DrMikeG/2023_pico_space_mushroom/Space_Mushroom___Full_6_DOFs_Space_Mouse_5739462/images/3dmouse.jpg

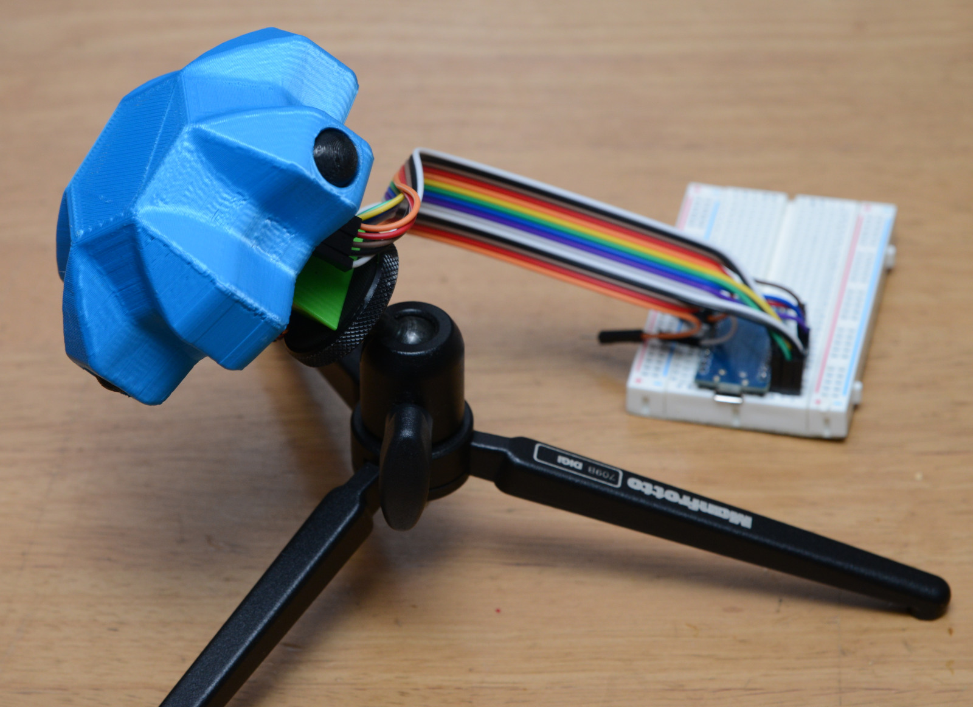
Space_Mushroom___Full_6_DOFs_Space_Mouse_5739462/images/3dmouse.jpg
