DrMikeG/2023_pico_space_mushroom/Space_Mushroom___Full_6_DOFs_Space_Mouse_5739462/images/_2022-12-24_12.27.17.jpg

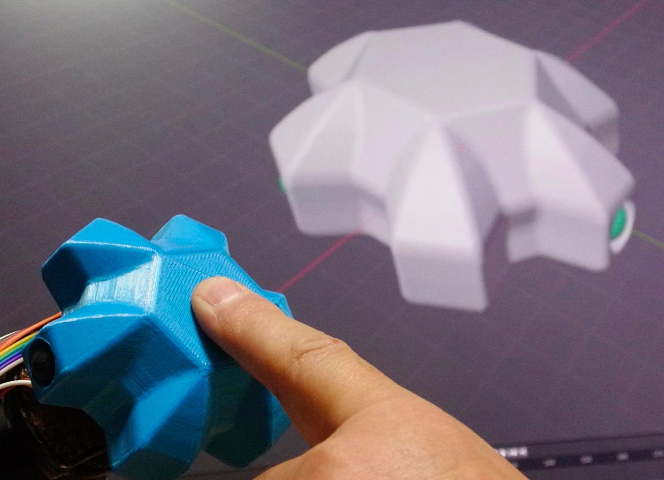
Space_Mushroom___Full_6_DOFs_Space_Mouse_5739462/images/_2022-12-24_12.27.17.jpg
