DrMikeG/2023_pico_space_mushroom/Space_Mushroom___Full_6_DOFs_Space_Mouse_5739462/images/ball-joint.png

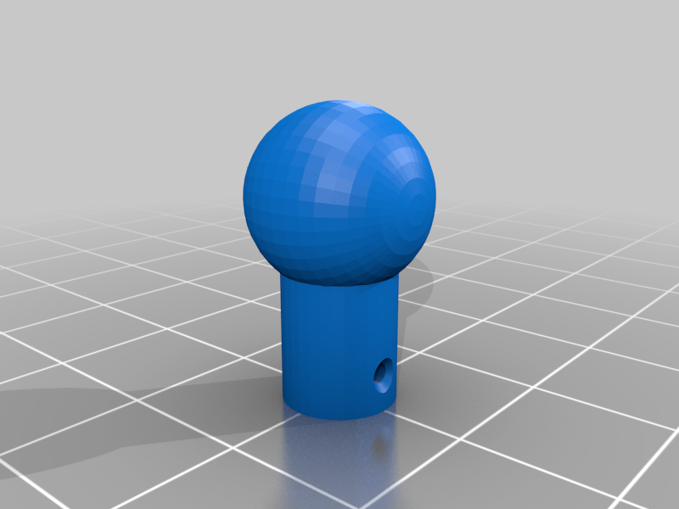
Space_Mushroom___Full_6_DOFs_Space_Mouse_5739462/images/ball-joint.png
