DrMikeG/2023_pico_space_mushroom/parts/mounting_lid_right_03.3mf

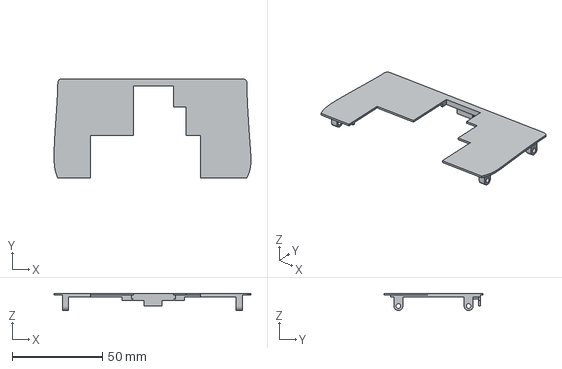
[picture p26: CAD file, 2023-02-21]
parts/mounting_lid_right_03.3mf
109.4 x 55.0 x 9.50 mm
