DrMikeG/2023_pico_space_mushroom/parts/Mounting_ADC_layer_04.3mf

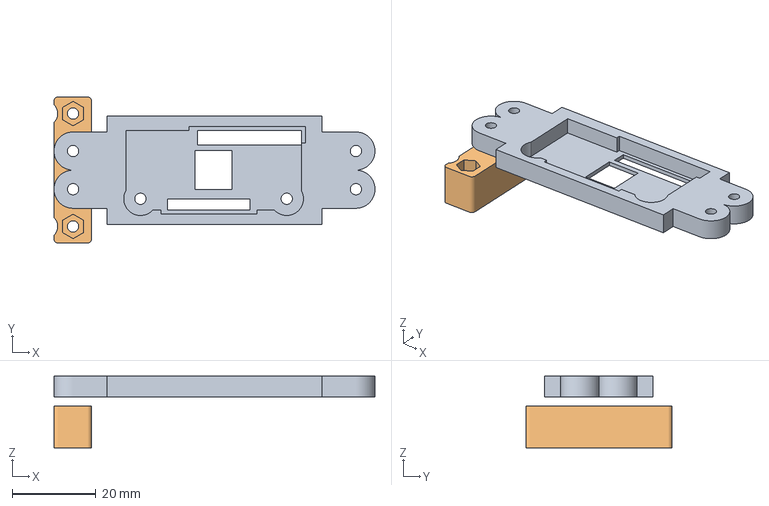
[picture p27: CAD file, 2023-02-15]
parts/Mounting_ADC_layer_04.3mf
76.8 x 35.0 x 17.2 mm
Mounting_ADC_layer_04 x 2
