DrMikeG/2023_pico_space_mushroom/parts/mounting_subbase_01.3mf

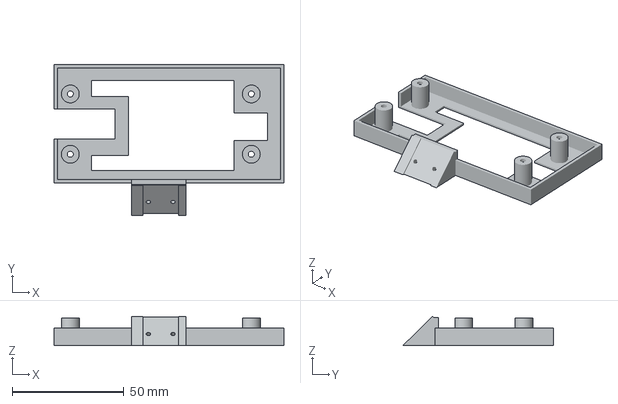
[picture p28: CAD file, 2023-02-15]
parts/mounting_subbase_01.3mf
103.0 x 67.4 x 13.2 mm
