DrMikeG/2023_pico_space_mushroom/parts/mounting_lid_right_02.3mf

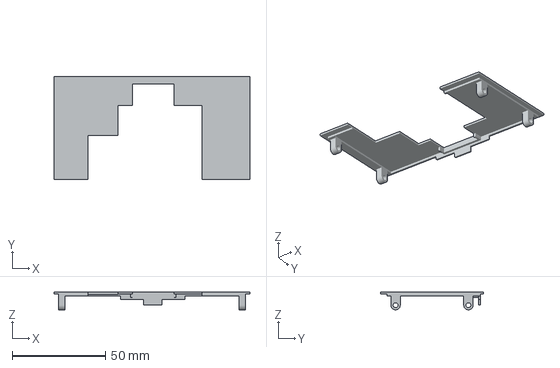
[picture p29: CAD file, 2023-02-15]
parts/mounting_lid_right_02.3mf
105.0 x 55.0 x 9.50 mm
