DrMikeG/2023_pico_space_mushroom/parts/Mounting_ProtoLayer00_01.3mf

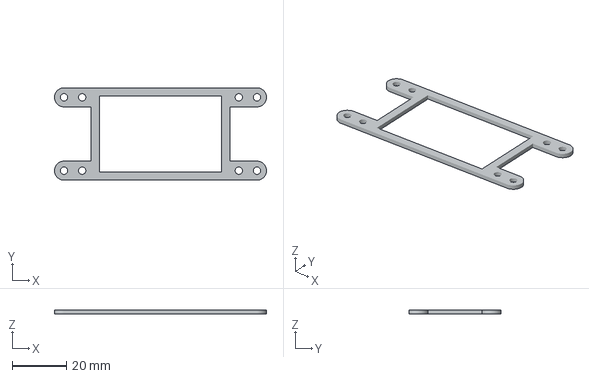
[picture p30: CAD file, 2023-02-15]
parts/Mounting_ProtoLayer00_01.3mf
78.1 x 34.0 x 1.50 mm
