DrMikeG/2023_pico_space_mushroom/parts/mounting_subbase_03.3mf

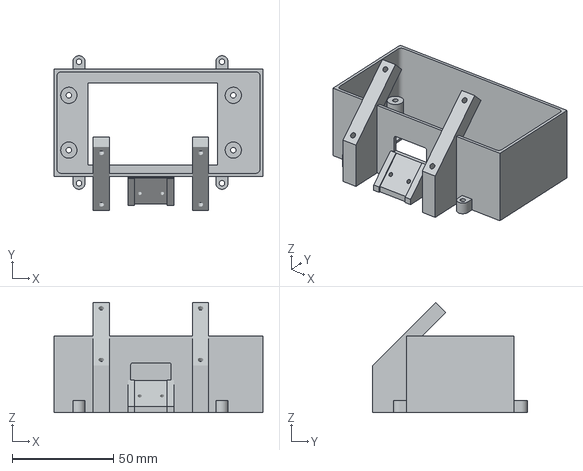
[picture p31: CAD file, 2023-02-15]
parts/mounting_subbase_03.3mf
103.0 x 76.3 x 54.3 mm
