DrMikeG/2023_pico_space_mushroom/parts/mounting_subbase_02.3mf

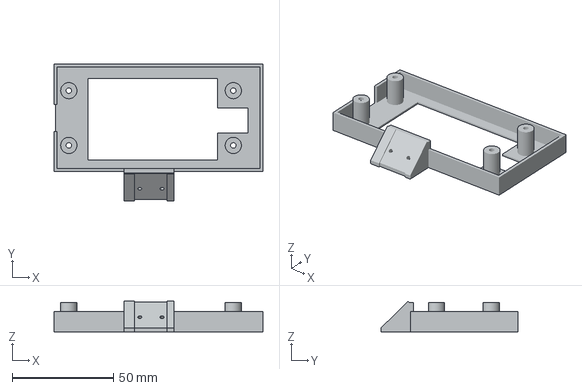
[picture p32: CAD file, 2023-02-15]
parts/mounting_subbase_02.3mf
103.0 x 67.4 x 15.2 mm
