DrMikeG/2023_pico_space_mushroom/parts/Mounting_ProtoLayer00_03.3mf

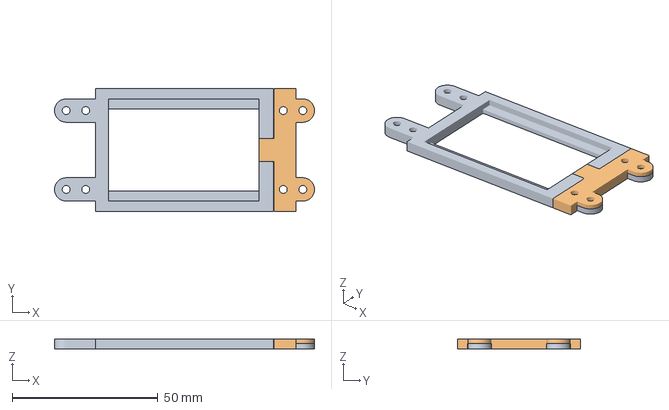
[picture p33: CAD file, 2023-02-15]
parts/Mounting_ProtoLayer00_03.3mf
89.1 x 42.0 x 3.50 mm
Mounting_ProtoLayer00_03 x 2
