DrMikeG/2023_pico_space_mushroom/parts/Mounting_ADC_layer_03.3mf

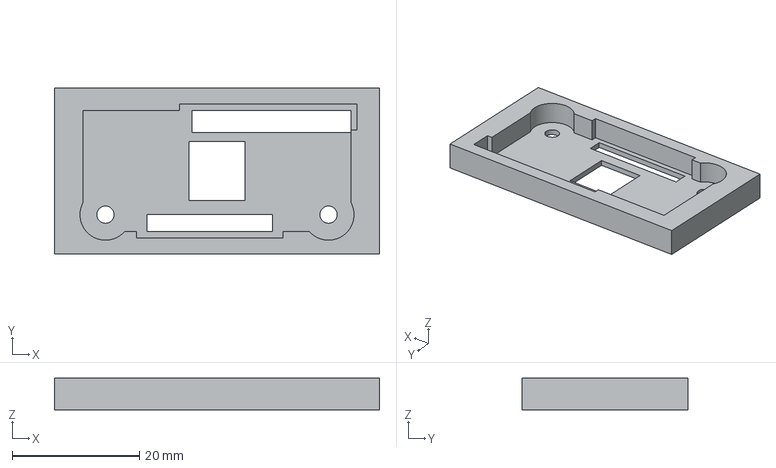
[picture p34: CAD file, 2023-02-15]
parts/Mounting_ADC_layer_03.3mf
51.0 x 26.0 x 5.00 mm
