DrMikeG/2023_pico_space_mushroom/parts/Mounting_ADC_layer_06.3mf

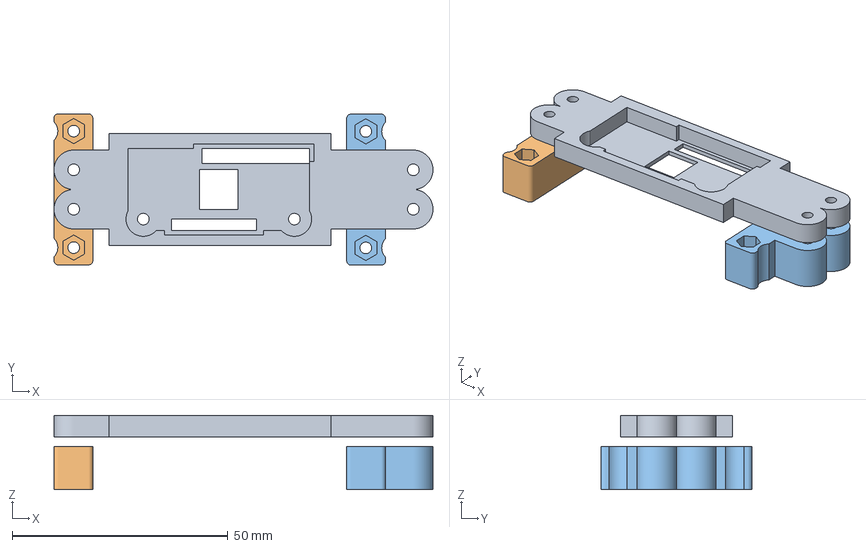
[picture p35: CAD file, 2023-02-15]
parts/Mounting_ADC_layer_06.3mf
87.8 x 35.1 x 17.2 mm
Mounting_ADC_layer_06 x 3
