DrMikeG/2023_pico_space_mushroom/parts/mounting_feet_01.3mf

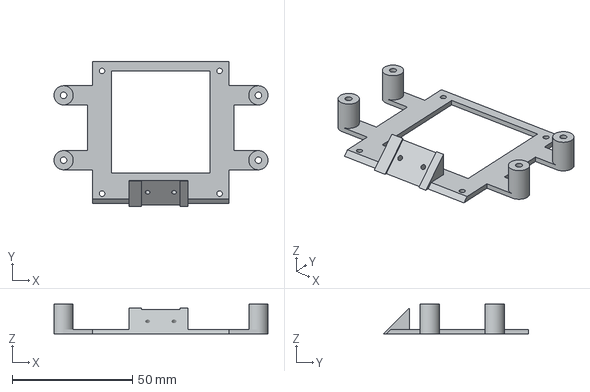
[picture p36: CAD file, 2023-02-15]
parts/mounting_feet_01.3mf
89.1 x 60.5 x 12.4 mm
