DrMikeG/2023_pico_space_mushroom/parts/mounting_subbase_04.3mf

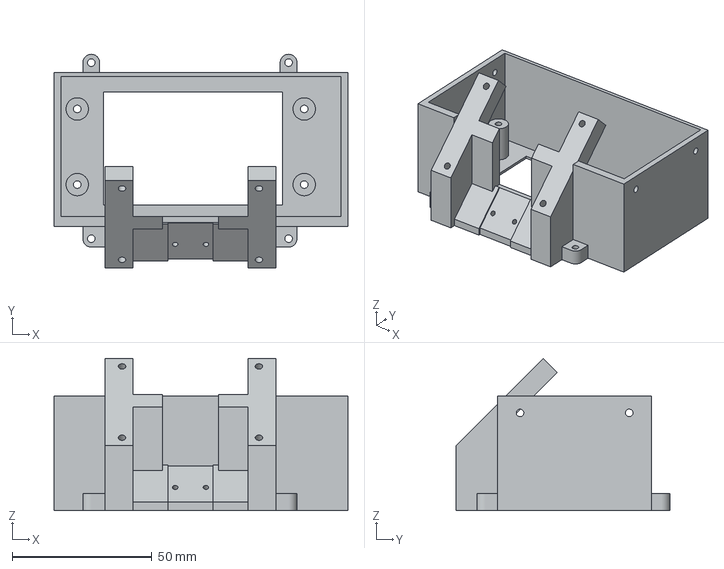
[picture p37: CAD file, 2023-02-15]
parts/mounting_subbase_04.3mf
105.0 x 76.3 x 54.3 mm
