DrMikeG/2023_pico_space_mushroom/parts/Mounting_ProtoLayer01_02.3mf

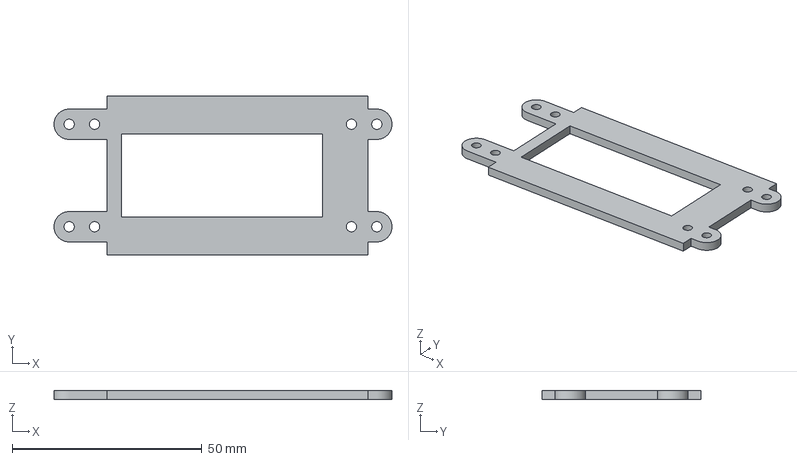
[picture p38: CAD file, 2023-02-15]
parts/Mounting_ProtoLayer01_02.3mf
89.1 x 42.0 x 2.50 mm
