DrMikeG/2023_pico_space_mushroom/parts/Mounting_ProtoLayer01_01.3mf

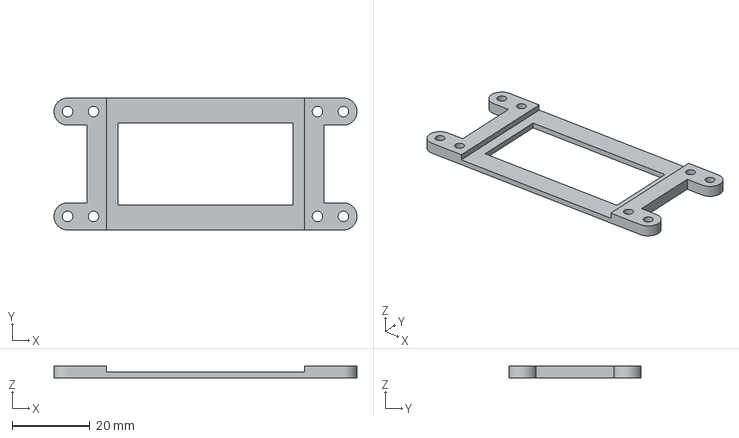
[picture p39: CAD file, 2023-02-15]
parts/Mounting_ProtoLayer01_01.3mf
78.1 x 34.0 x 3.10 mm
