DrMikeG/2023_pico_space_mushroom/parts/mounting_lid_right_01.3mf

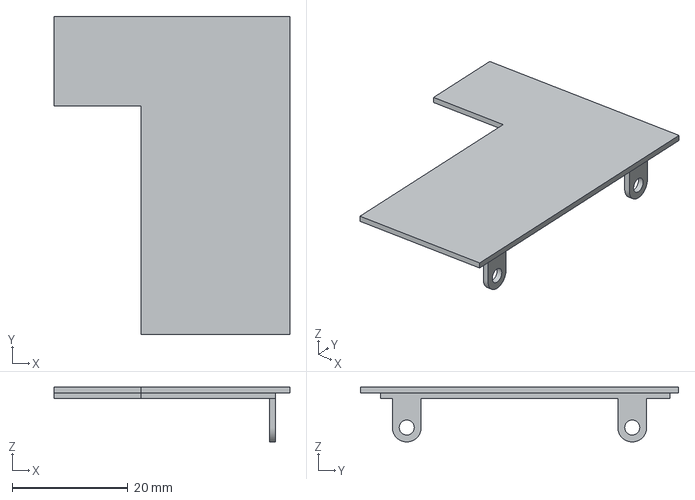
[picture p40: CAD file, 2023-02-15]
parts/mounting_lid_right_01.3mf
40.8 x 55.0 x 9.50 mm
