DrMikeG/2023_pico_space_mushroom/parts/Mounting_ProtoLayer00_02.3mf

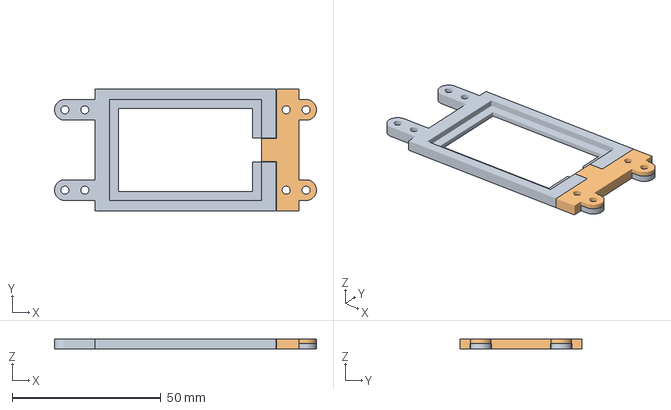
[picture p41: CAD file, 2023-02-15]
parts/Mounting_ProtoLayer00_02.3mf
88.1 x 41.0 x 3.50 mm
Mounting_ProtoLayer00_02 x 2
