DrMikeG/2023_pico_space_mushroom/parts/led_mount_03.3mf

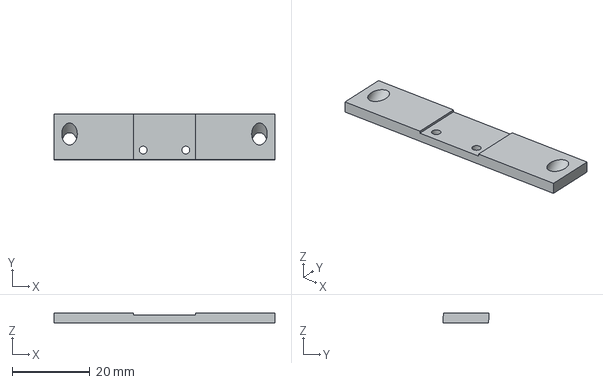
[picture p42: CAD file, 2023-02-02]
parts/led_mount_03.3mf
56.9 x 11.7 x 2.53 mm
