DrMikeG/2023_pico_space_mushroom/parts/min_base_support_02.3mf

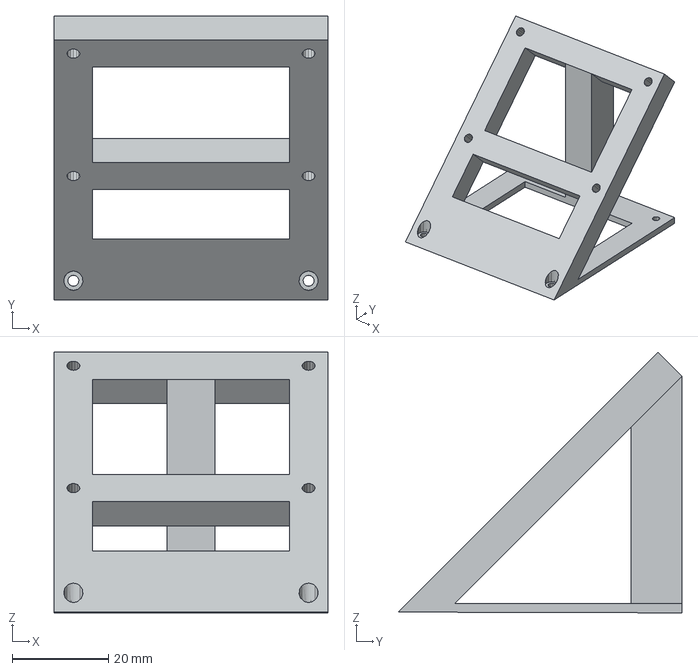
[picture p43: CAD file, 2023-01-13]
parts/min_base_support_02.3mf
56.9 x 59.1 x 54.2 mm
