DrMikeG/2023_pico_space_mushroom/parts/Thumbstick.3mf

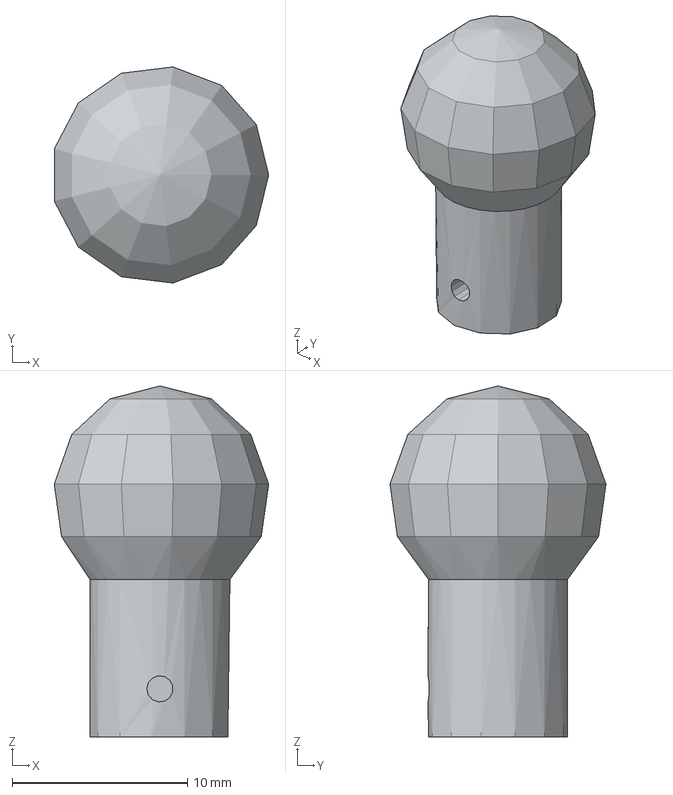
[picture p44: CAD file, 2023-01-13]
parts/Thumbstick.3mf
12.3 x 12.3 x 20.1 mm
