DrMikeG/2023_pico_space_mushroom/parts/minimal_base.stl

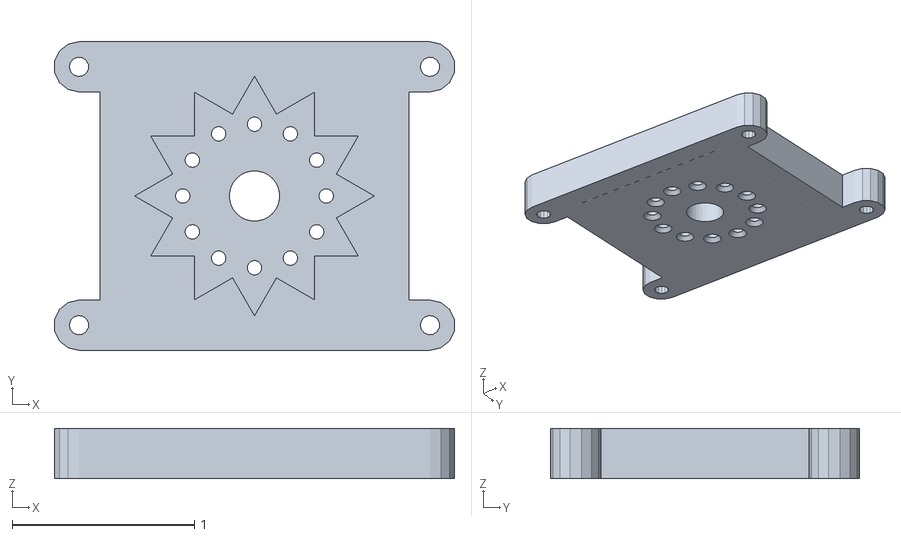
[picture p45: CAD file, 2023-01-13]
parts/minimal_base.stl
2.19 x 1.69 x 0.277
