DrMikeG/2023_pico_space_mushroom/parts/minimal_base_remade.3mf

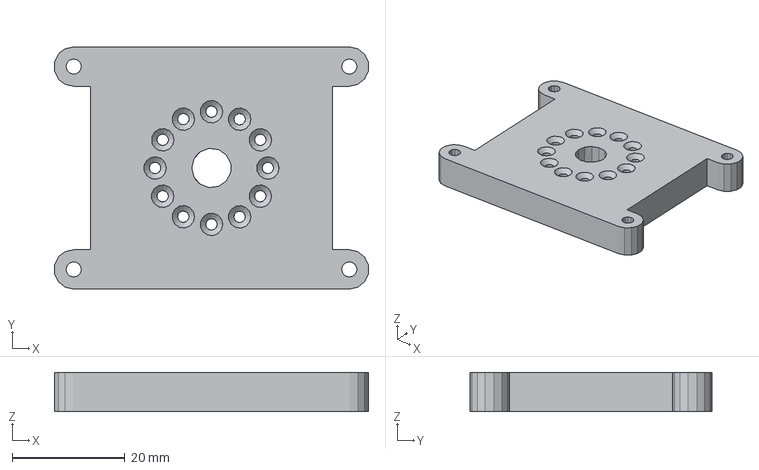
[picture p46: CAD file, 2023-01-13]
parts/minimal_base_remade.3mf
55.7 x 43.0 x 7.00 mm
