DrMikeG/2023_pico_space_mushroom/parts/Thumbstick_fine.3mf

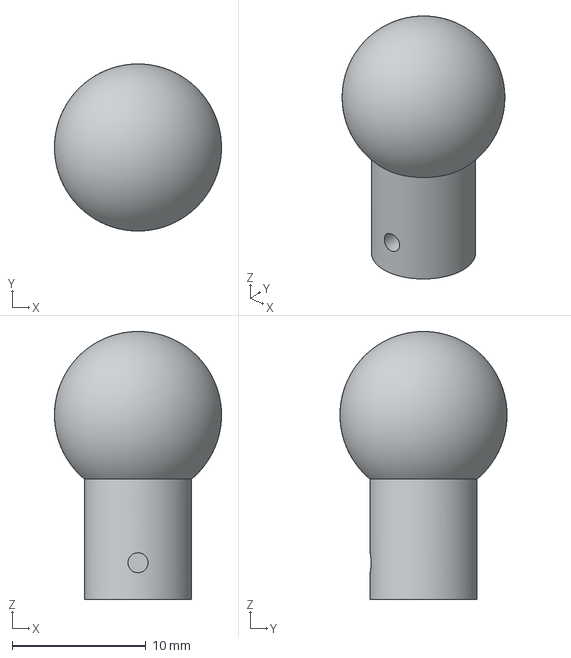
[picture p47: CAD file, 2023-01-13]
parts/Thumbstick_fine.3mf
12.5 x 12.5 x 20.1 mm
