DrMikeG/2023_pico_space_mushroom/code/11_mouseDebugging/2023-02-18_22-02-50.gif

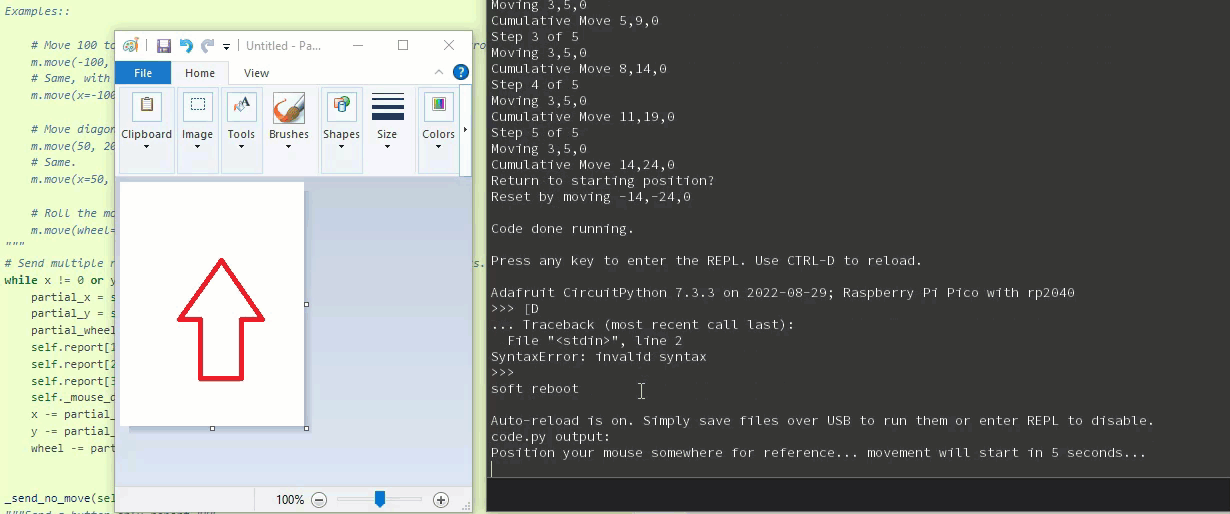
code/11_mouseDebugging/2023-02-18_22-02-50.gif
