DrMikeG/2023_pico_space_mushroom/code/11_mouseDebugging/2023-02-18_22-15-18.gif

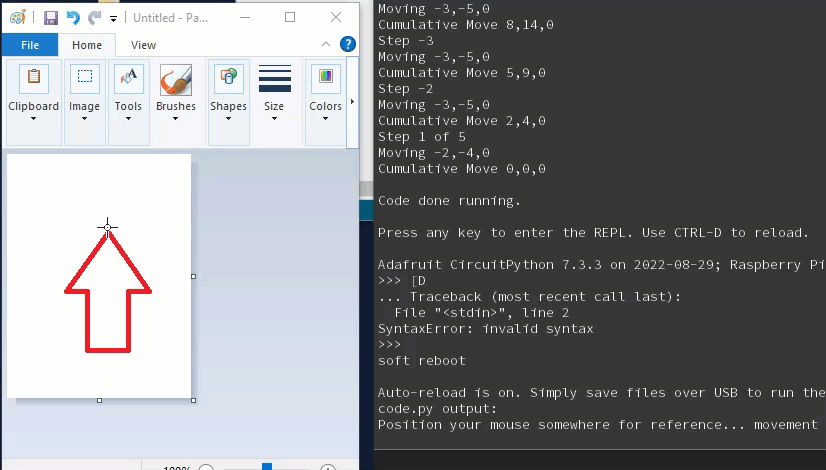
code/11_mouseDebugging/2023-02-18_22-15-18.gif
