DrMikeG/2023_pico_space_mushroom/code/11_mouseDebugging/excel.png

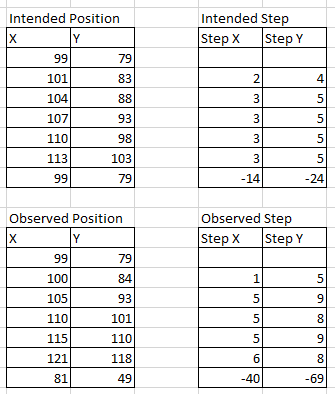
code/11_mouseDebugging/excel.png
